74th/dive9-buildguide/picture/keycap_v1.0.1.jpg

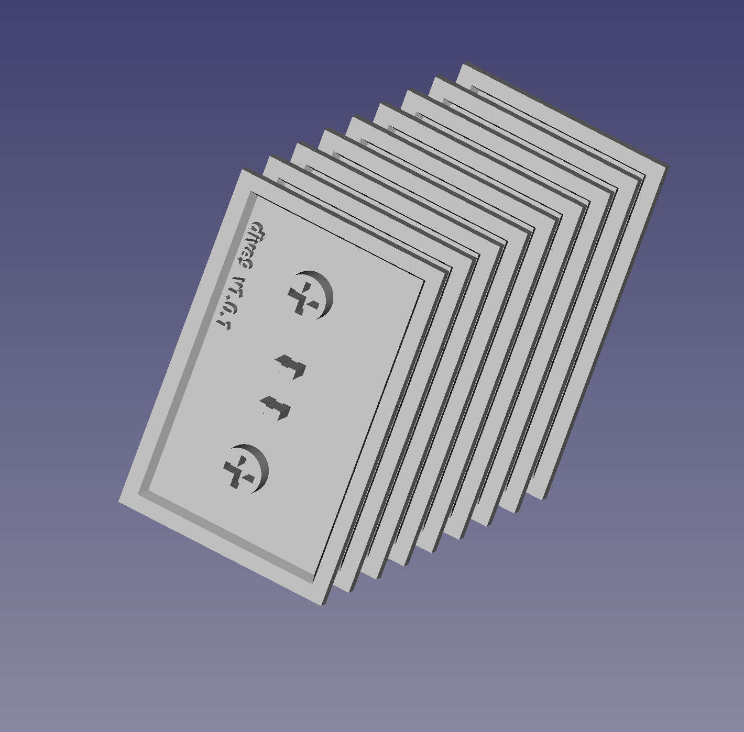
picture/keycap_v1.0.1.jpg
